uditagarwal97/CANSAT-18-TEAM_KALPANA_1/GCS_VIEW/images/2426.png

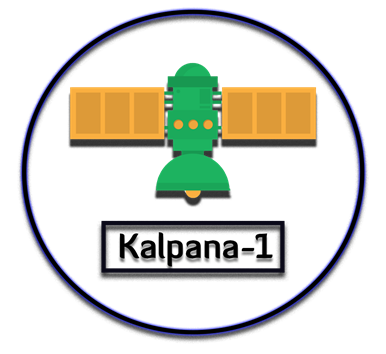
GCS_VIEW/images/2426.png
